DWShuo/simulacra-DM/simulacra/keymaps/default/config.h

#pragma once

#define USE_SERIAL

#define EE_HANDS
// #define MASTER_LEFT
// #define MASTER_RIGHT
// Rows are doubled-up

#define ENCODER_RESOLUTION 4

#define OLED_TIMEOUT 600000 // 10 minutes
#define OLED_BRIGHTNESS 50
